spspider/EcoLogic-KiCad/IoTmanager/images/8iGbkG6rT.jpg

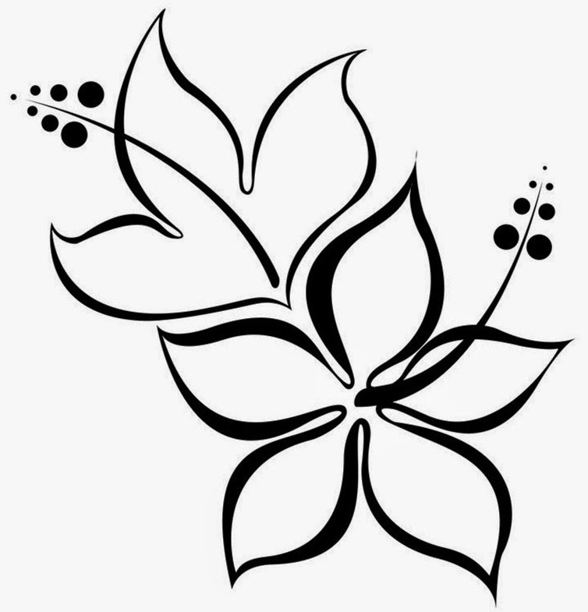
IoTmanager/images/8iGbkG6rT.jpg
