spspider/EcoLogic-KiCad/IoTmanager/images/979dd874542591.5c33740e54a3a.webp

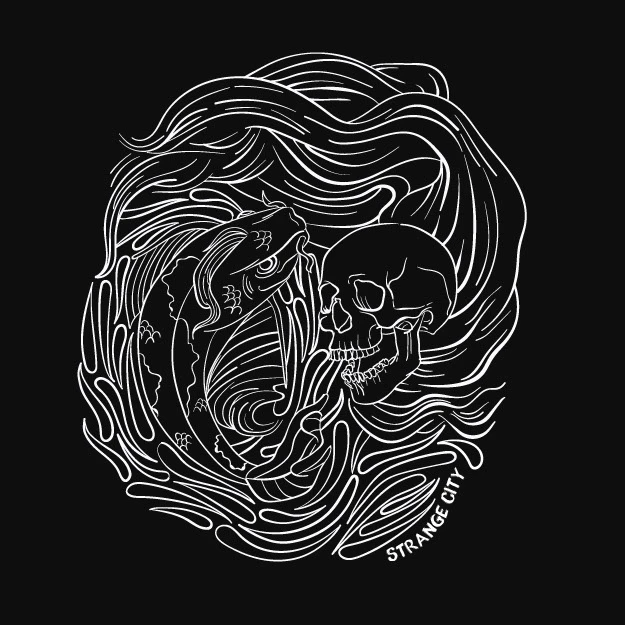
IoTmanager/images/979dd874542591.5c33740e54a3a.webp
