spspider/EcoLogic-KiCad/IoTmanager/images/black-and-white-line-drawing-of-two-girls-wearing-flower-crowns-facing-each-other-with-their-noses-touching-vector.jpg

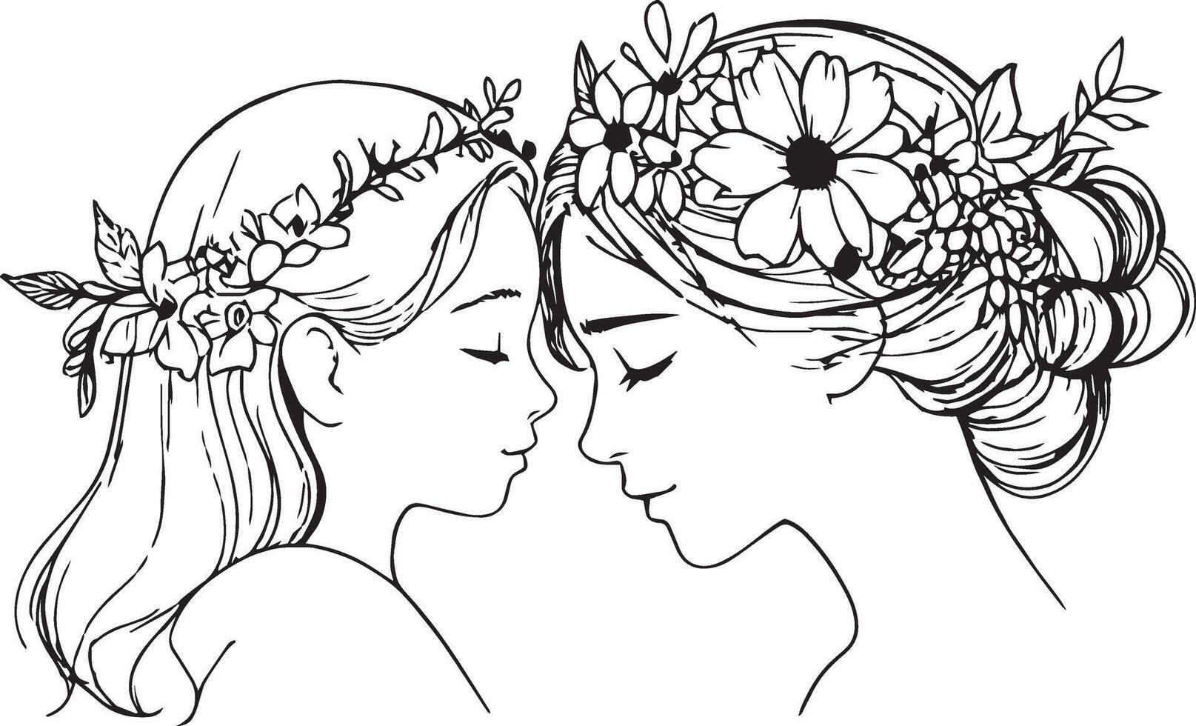
IoTmanager/images/black-and-white-line-drawing-of-two-girls-wearing-flower-crowns-facing-each-other-with-their-noses-touching-vector.jpg
