spspider/EcoLogic-KiCad/IoTmanager/images/czNmcy1wcml2YXRlL3Jhd3BpeGVsX2ltYWdlcy93ZWJzaXRlX2NvbnRlbnQvam9iNjY4LTExNy1wXzEtbDE0YWw5ZGsucG5n.webp

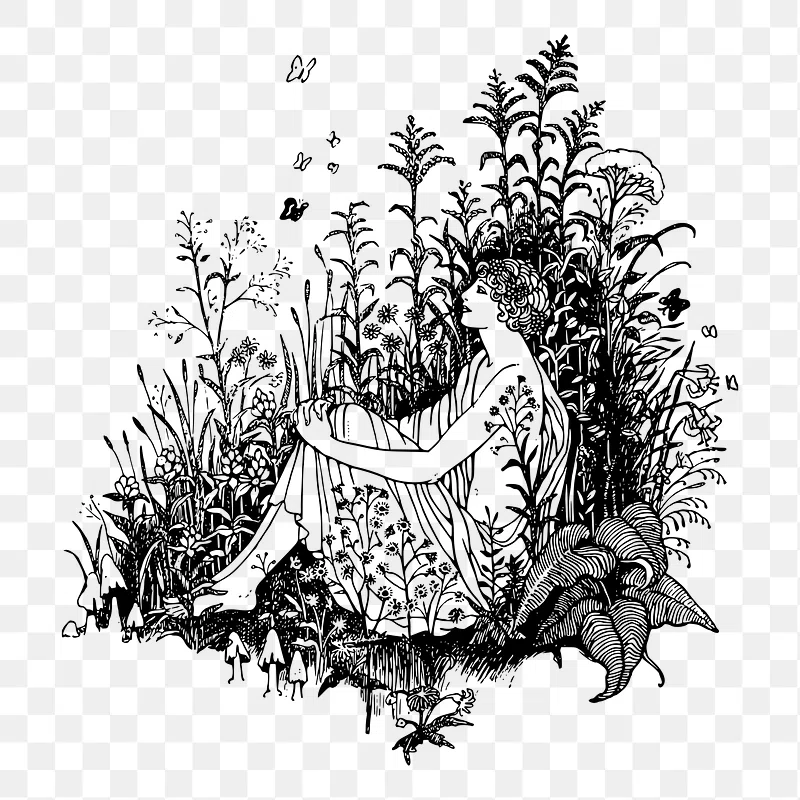
IoTmanager/images/czNmcy1wcml2YXRlL3Jhd3BpeGVsX2ltYWdlcy93ZWJzaXRlX2NvbnRlbnQvam9iNjY4LTExNy1wXzEtbDE0YWw5ZGsucG5n.webp
