spspider/EcoLogic-KiCad/IoTmanager/images/Gemini_Generated_Image_persy7persy7pers.png

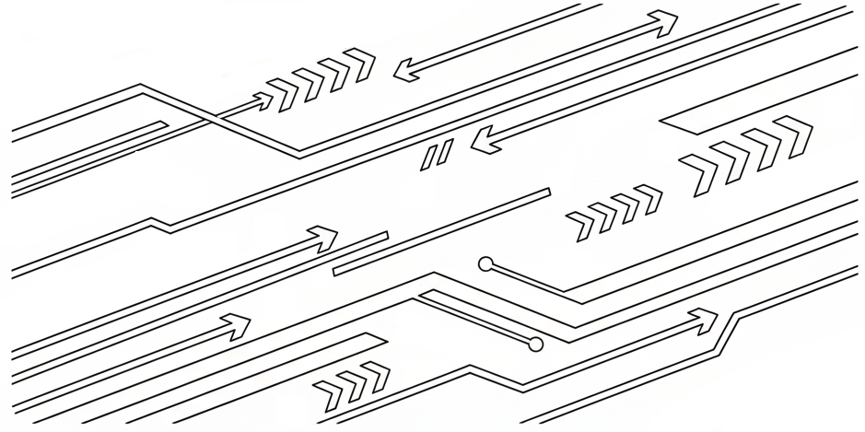
IoTmanager/images/Gemini_Generated_Image_persy7persy7pers.png
