spspider/EcoLogic-KiCad/IoTmanager/images/Gemini_Generated_Image_qw4ks4qw4ks4qw4k.png

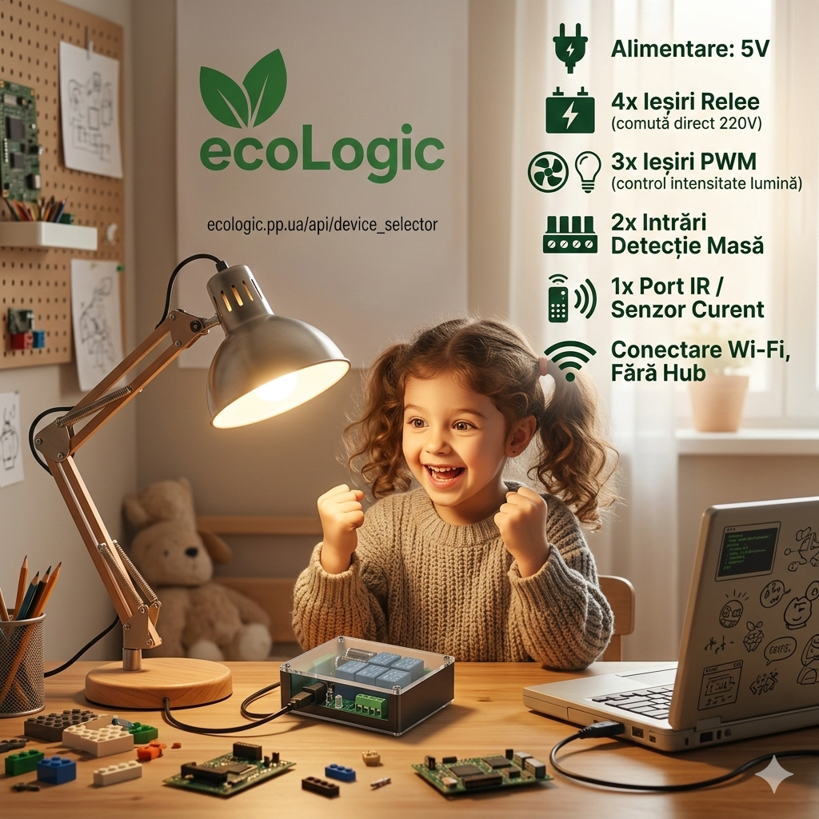
IoTmanager/images/Gemini_Generated_Image_qw4ks4qw4ks4qw4k.png
