spspider/EcoLogic-KiCad/IoTmanager/images/Gemini_Generated_Image_z5fgx4z5fgx4z5fg.png

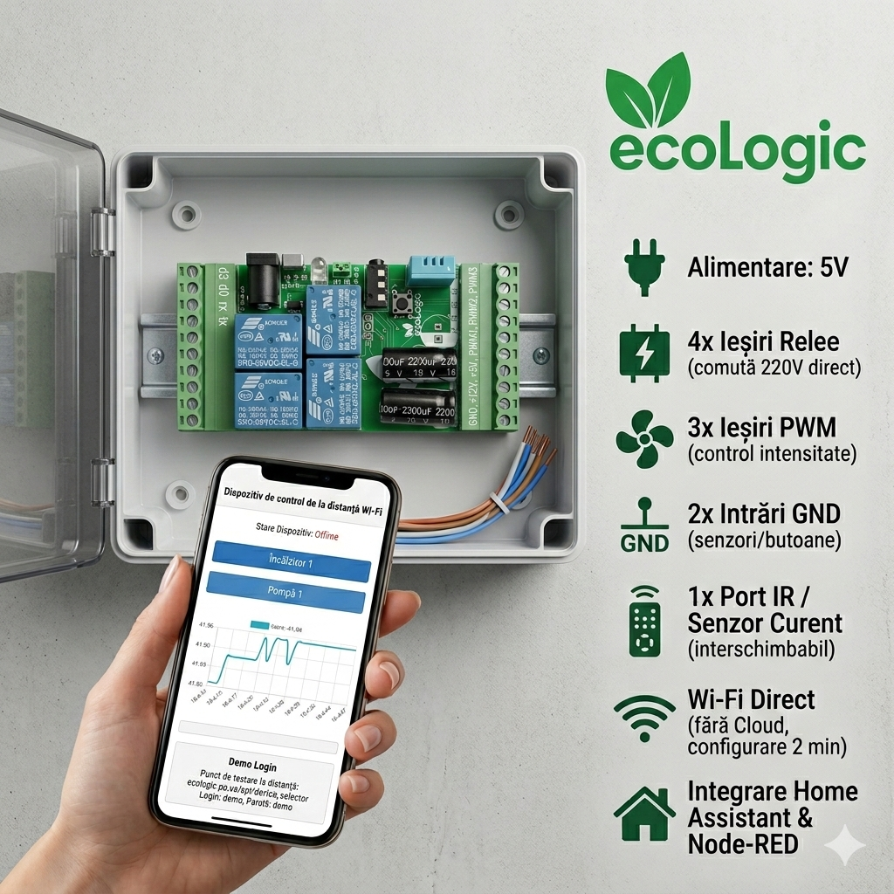
IoTmanager/images/Gemini_Generated_Image_z5fgx4z5fgx4z5fg.png
