spspider/EcoLogic-KiCad/IoTmanager/images/leaves.png

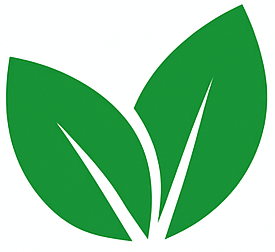
IoTmanager/images/leaves.png
