spspider/EcoLogic-KiCad/IoTmanager/images/lines.jpg

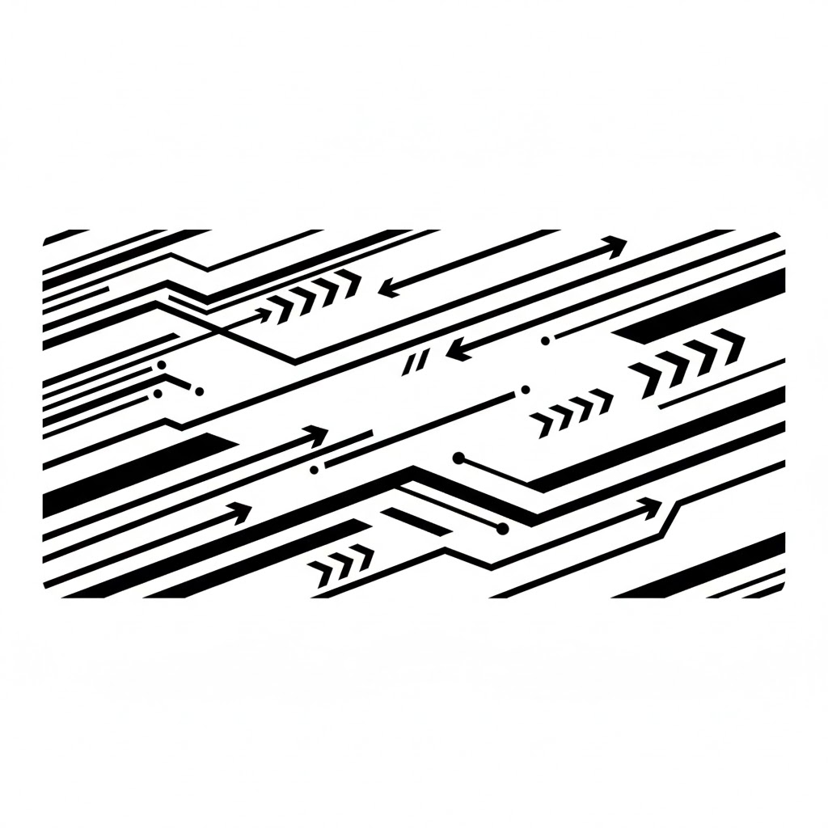
IoTmanager/images/lines.jpg
