spspider/EcoLogic-KiCad/IoTmanager/images/pcbway-onluneviewer.jpg

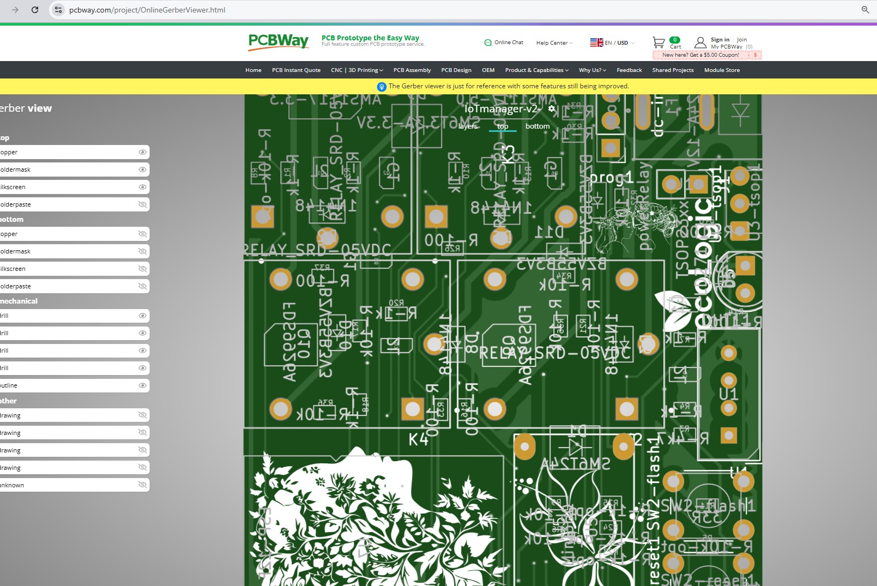
IoTmanager/images/pcbway-onluneviewer.jpg
