spspider/EcoLogic-KiCad/IoTmanager/scheme-instructions/baker.jpg

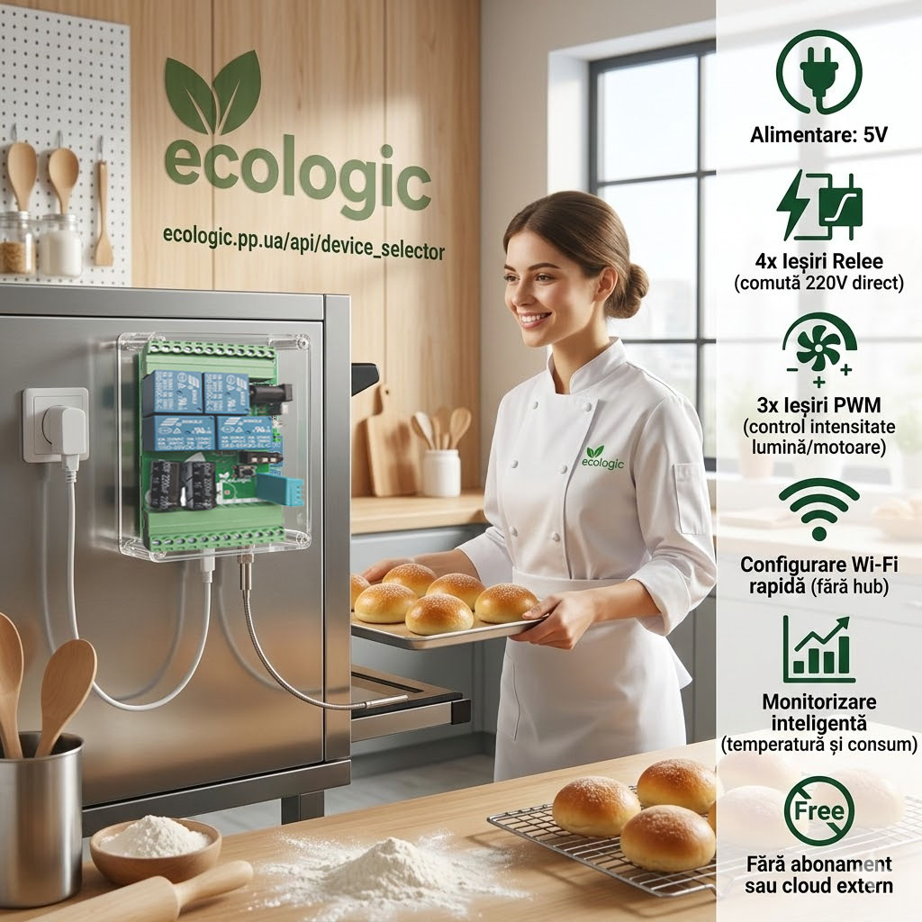
IoTmanager/scheme-instructions/baker.jpg
