spspider/EcoLogic-KiCad/IoTmanager/scheme-instructions/ecologic-boiler.png

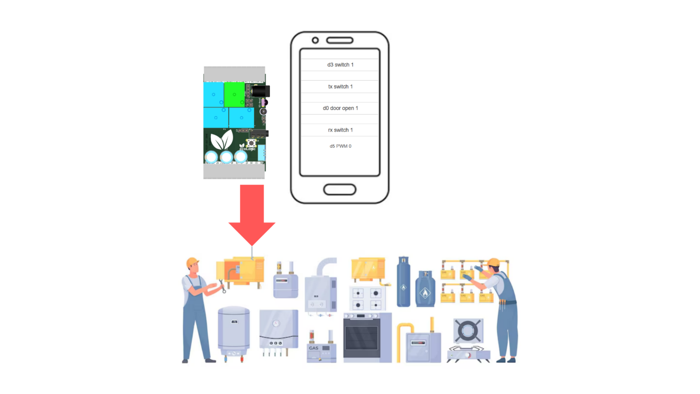
IoTmanager/scheme-instructions/ecologic-boiler.png
