spspider/EcoLogic-KiCad/IoTmanager/scheme-instructions/ecologic-door.png

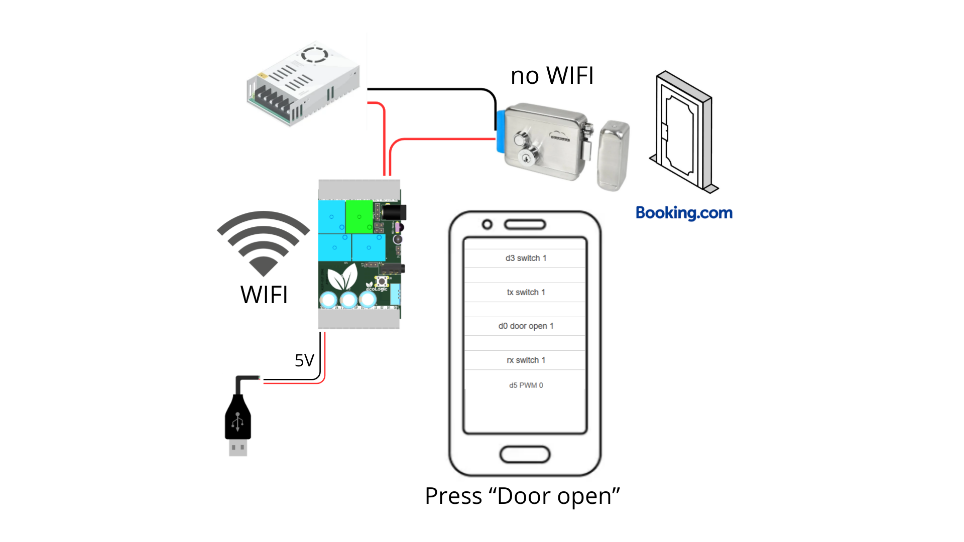
IoTmanager/scheme-instructions/ecologic-door.png
