spspider/EcoLogic-KiCad/IoTmanager/scheme-instructions/ecologic-gate.png

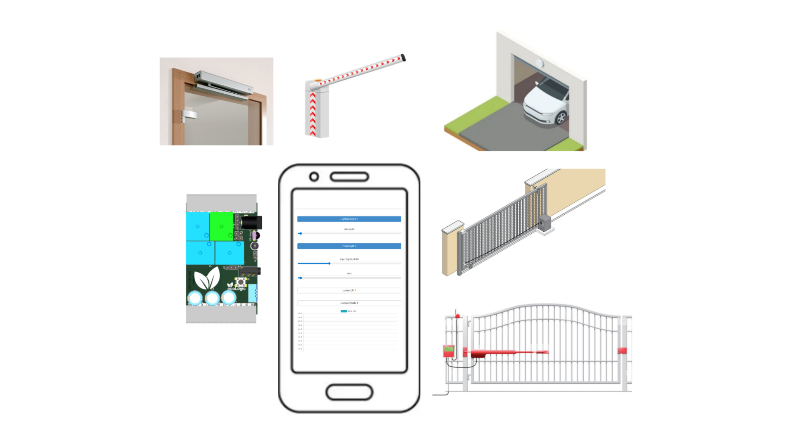
IoTmanager/scheme-instructions/ecologic-gate.png
