spspider/EcoLogic-KiCad/IoTmanager/scheme-instructions/IOT-scheme-instruction.drawio1.png

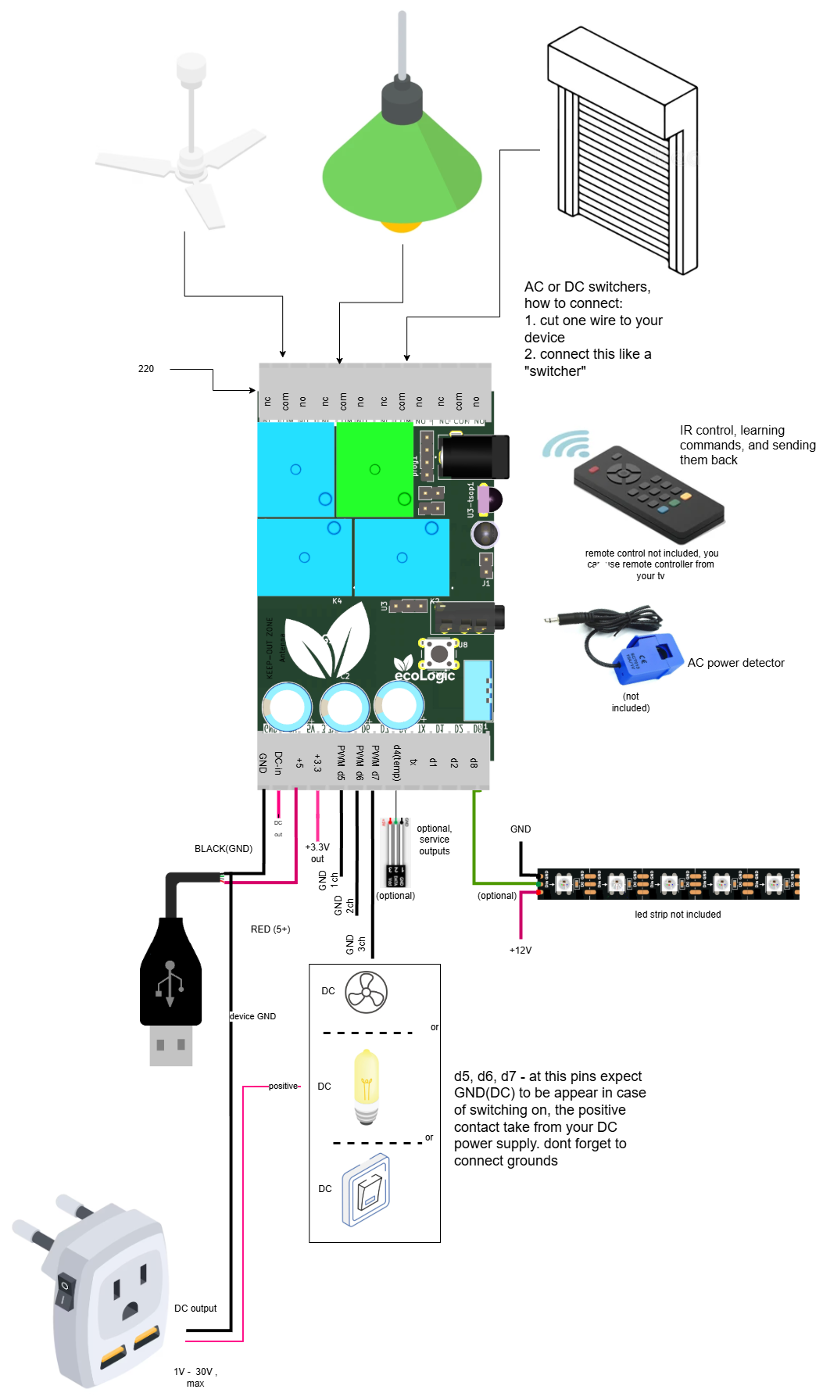
IoTmanager/scheme-instructions/IOT-scheme-instruction.drawio1.png
