spspider/EcoLogic-KiCad/IoTmanager/scheme-instructions/IOT-scheme-instruction.drawio.png

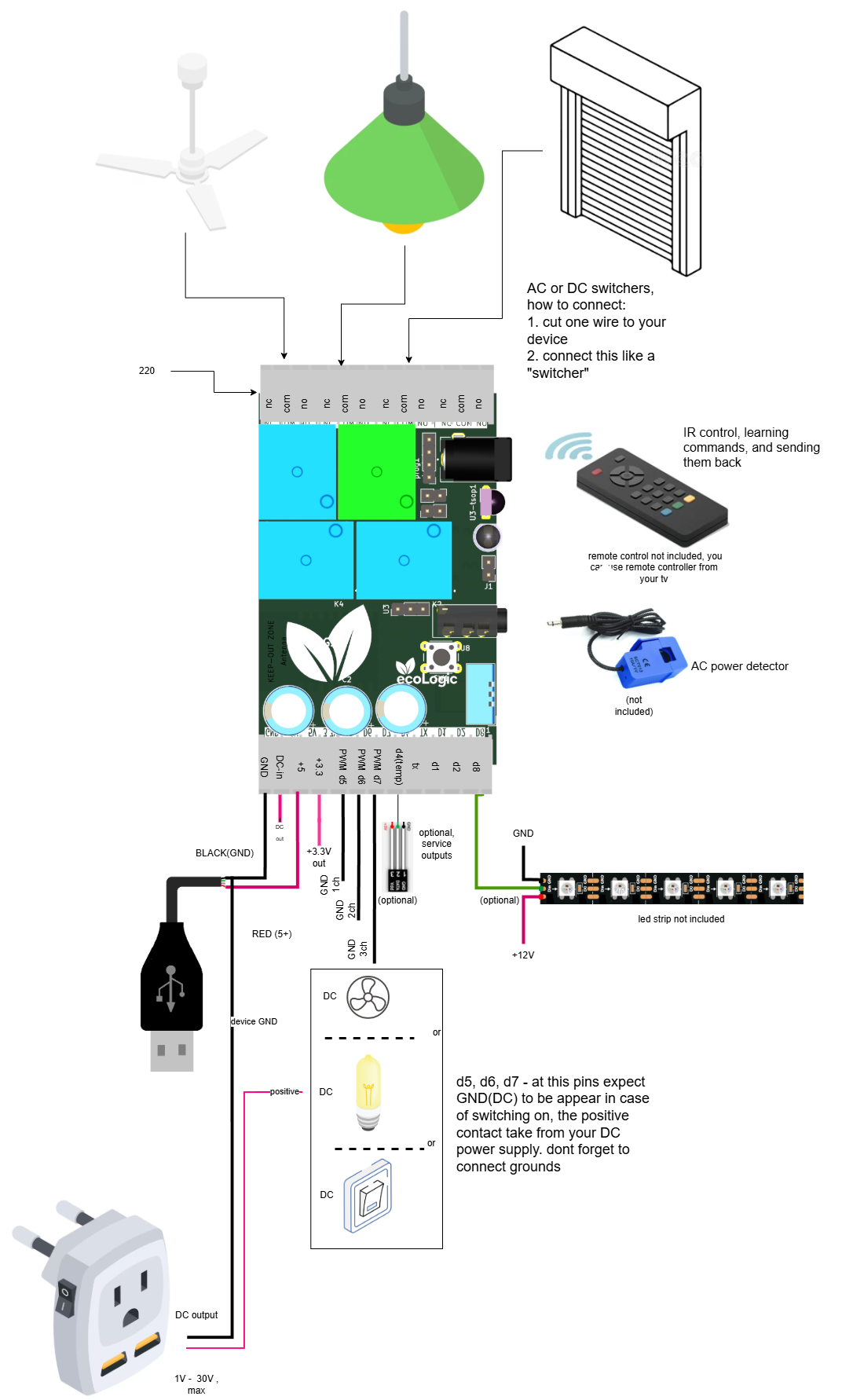
IoTmanager/scheme-instructions/IOT-scheme-instruction.drawio.png
