spspider/EcoLogic-KiCad/IoTmanager/scheme-instructions/Снимок экрана 2026-03-01 180455.png

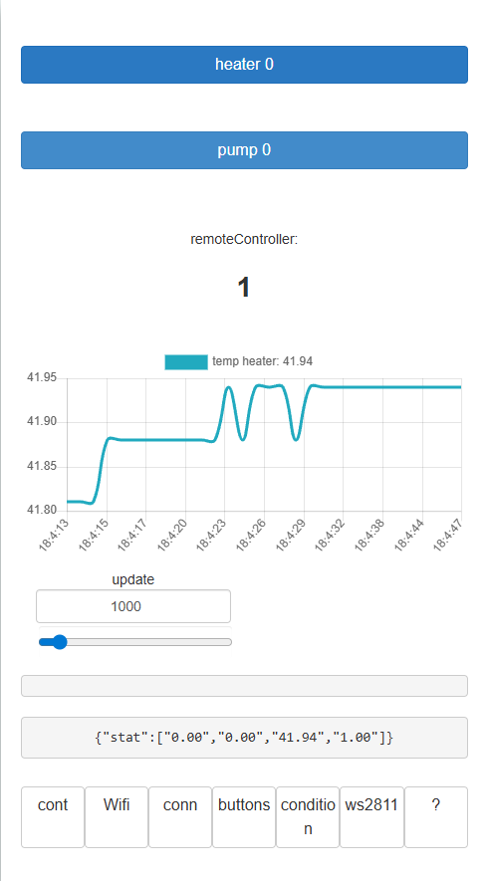
IoTmanager/scheme-instructions/Снимок экрана 2026-03-01 180455.png
